helmitikka/tietotekniikan_sovellusprojekti/Dokumentit/3D-mallit/3d-malli-kansi.jpg

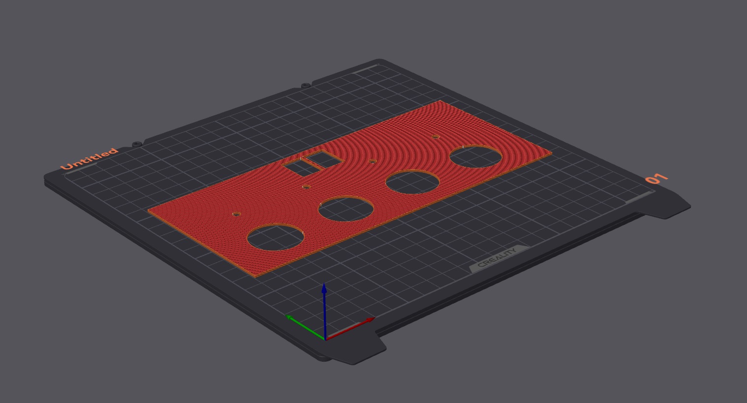
Dokumentit/3D-mallit/3d-malli-kansi.jpg
